ttdgp6b7sy-ai/oxide-keys/cad/base-plate.step

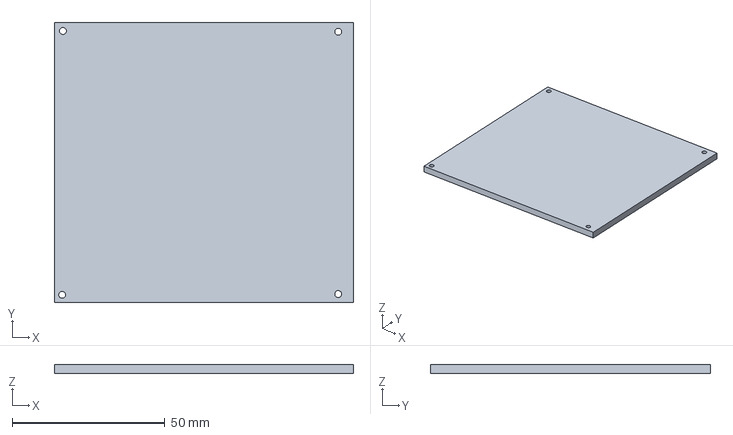
[picture p21: CAD file, 2026-09-26]
cad/base-plate.step
97.8 x 91.5 x 3.00 mm
