ttdgp6b7sy-ai/oxide-keys/cad/switch-deck.step

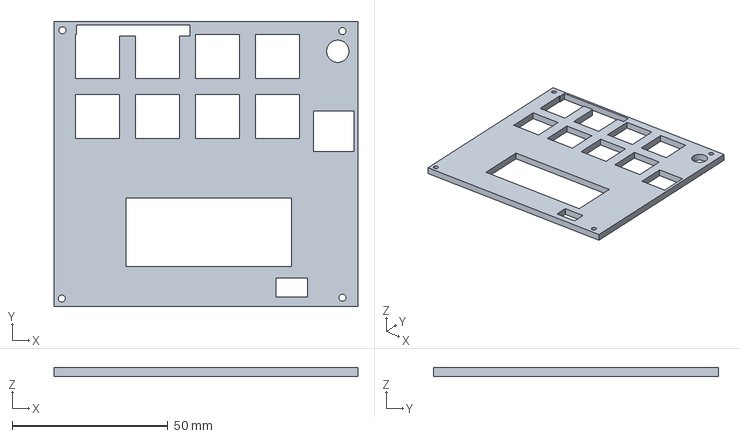
[picture p22: CAD file, 2026-09-26]
cad/switch-deck.step
97.8 x 91.5 x 3.00 mm
