ttdgp6b7sy-ai/oxide-keys/cad/pcbfirstdesign.step

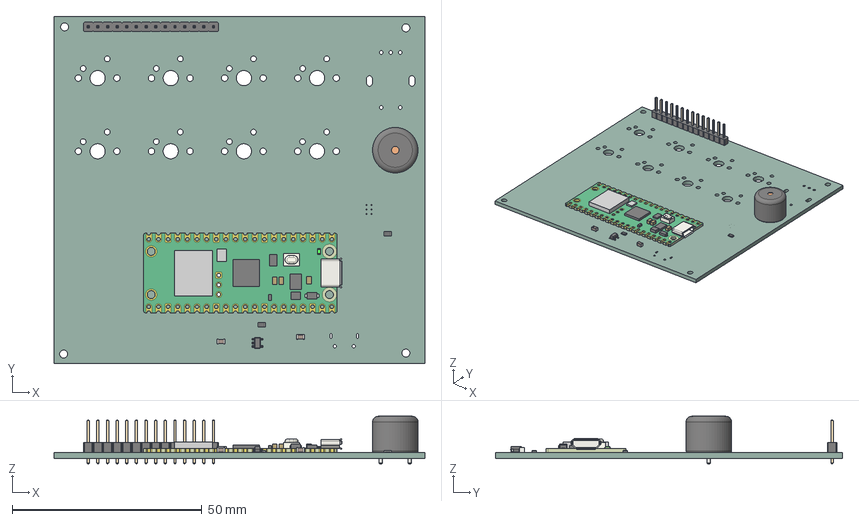
[picture p23: CAD file, 2026-09-26]
cad/pcbfirstdesign.step
97.8 x 91.5 x 12.5 mm
PinHeader_1x14_P254mm_Vertical
SOT-23-5
R_0805_2012Metric x 2
Buzzer_12x95RM76
RaspberryPi_Pico_W_Module_KiCad
C_0805_2012Metric x 2
pcbfirstdesign-unsaved-export-nXNS2h_PCB
